z2034831520/FunModularKeyboard-Numpad/doc/image1.png

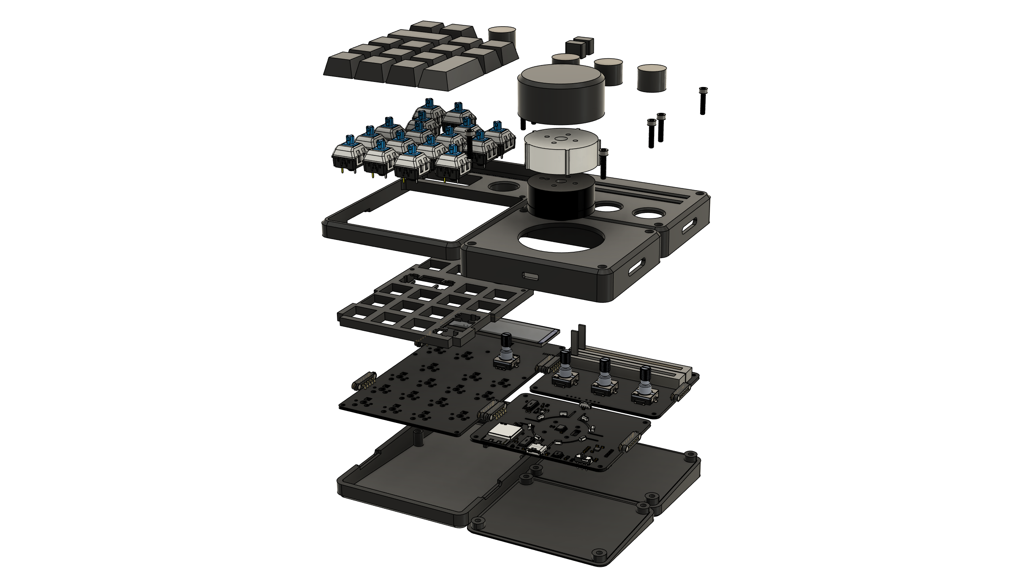
doc/image1.png
