z2034831520/FunModularKeyboard-Numpad/doc/image3.png

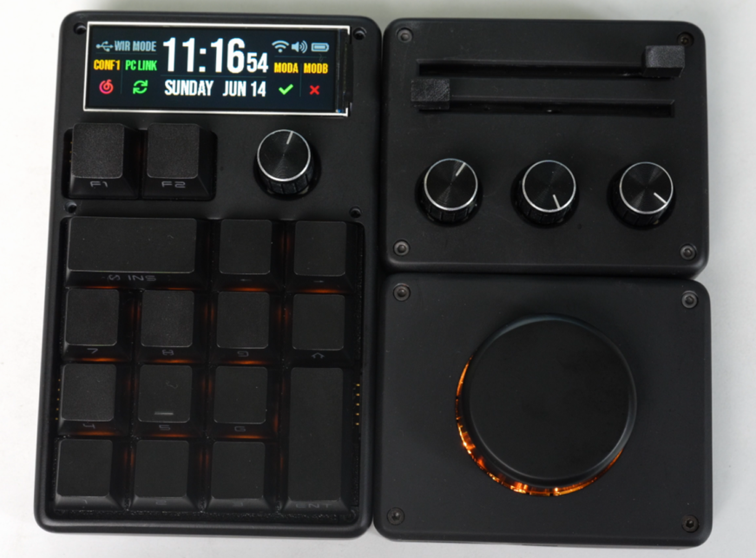
doc/image3.png
