z2034831520/FunModularKeyboard-Numpad/doc/image5.png

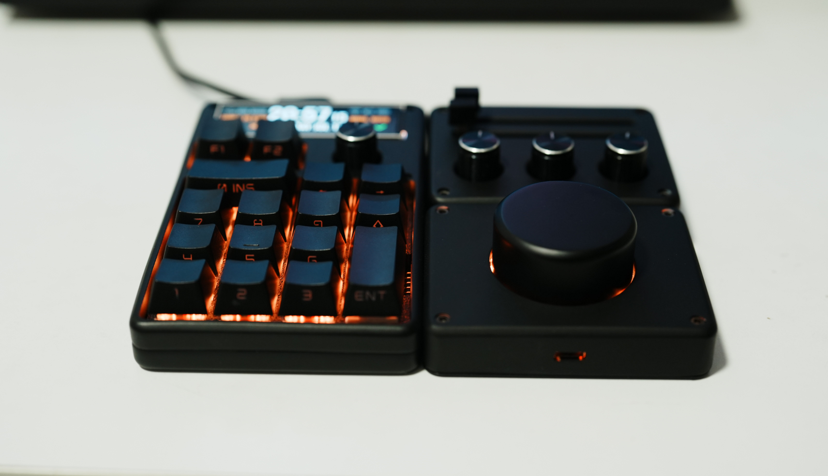
doc/image5.png
