z2034831520/FunModularKeyboard-Numpad/firmware/FunModularKeyboard/src/lvgl_setup.cpp

#include "lvgl_setup.h"
#include "display_config.h"
#include "nv3007_init.h"
#include <Arduino.h>
#include <lvgl.h>
#include <SPIFFS.h>
#include <TFT_eSPI.h>

namespace
{
    constexpr uint8_t kTftBacklightPwmChannel = 7;
    // Keep the LEDC configuration inside the ESP32-S3 timing budget.
    constexpr uint32_t kTftBacklightPwmFrequency = 5000;
    constexpr uint8_t kTftBacklightPwmResolution = 12;

    TFT_eSPI s_lcd;
    bool s_backlight_pwm_ready = false;
    bool s_tft_ready = false;
    bool s_spiffs_fs_registered = false;

    void nv3007_write_command(uint8_t command, const uint8_t *parameters, uint8_t parameter_count)
    {
        s_lcd.writecommand(command);
        for (uint8_t index = 0; index < parameter_count; ++index)
        {
            s_lcd.writedata(parameters[index]);
        }
    }

    void nv3007_initialize()
    {
        // TFT_eSPI initializes the SPI peripheral for us. Reset once more so the
        // generic bootstrap is discarded before applying the NV3007 sequence.
        pinMode(display_config::kResetPin, OUTPUT);
        digitalWrite(display_config::kResetPin, HIGH);
        delay(10);
        digitalWrite(display_config::kResetPin, LOW);
        delay(120);
        digitalWrite(display_config::kResetPin, HIGH);
        delay(120);

        s_lcd.startWrite();
        nv3007_write_command(0x28, nullptr, 0); // Display off during setup
        size_t position = 0;
        while (position < nv3007::kInitCommandsSize)
        {
            const uint8_t command = nv3007::kInitCommands[position++];
            const uint8_t parameter_count = nv3007::kInitCommands[position++];
            nv3007_write_command(command, &nv3007::kInitCommands[position], parameter_count);
            position += parameter_count;
        }
        nv3007_write_command(0x11, nullptr, 0); // Sleep out
        s_lcd.endWrite();
        delay(120);

        s_lcd.startWrite();
        const uint8_t landscape_rotation = 0x60; // MX | MV | RGB
        nv3007_write_command(0x36, &landscape_rotation, 1);
        s_lcd.endWrite();
    }

    String lvgl_spiffs_real_path(const char *path)
    {
        if (path == nullptr || path[0] == '\0')
        {
            return String("/");
        }
        if (path[0] == '/')
        {
            return String(path);
        }
        return String("/") + String(path);
    }

    void *lvgl_spiffs_open_cb(lv_fs_drv_t *drv, const char *path, lv_fs_mode_t mode)
    {
        LV_UNUSED(drv);
        const char *openMode = (mode == LV_FS_MODE_WR) ? FILE_WRITE : FILE_READ;
        File file = SPIFFS.open(lvgl_spiffs_real_path(path), openMode);
        if (!file)
        {
            return nullptr;
        }
        return new File(file);
    }

    lv_fs_res_t lvgl_spiffs_close_cb(lv_fs_drv_t *drv, void *file_p)
    {
        LV_UNUSED(drv);
        if (file_p == nullptr)
        {
            return LV_FS_RES_INV_PARAM;
        }
        File *file = static_cast<File *>(file_p);
        file->close();
        delete file;
        return LV_FS_RES_OK;
    }

    lv_fs_res_t lvgl_spiffs_read_cb(lv_fs_drv_t *drv, void *file_p, void *buf, uint32_t btr, uint32_t *br)
    {
        LV_UNUSED(drv);
        if (file_p == nullptr || buf == nullptr || br == nullptr)
        {
            return LV_FS_RES_INV_PARAM;
        }
        File *file = static_cast<File *>(file_p);
        *br = file->read(static_cast<uint8_t *>(buf), btr);
        return LV_FS_RES_OK;
    }

    lv_fs_res_t lvgl_spiffs_seek_cb(lv_fs_drv_t *drv, void *file_p, uint32_t pos, lv_fs_whence_t whence)
    {
        LV_UNUSED(drv);
        if (file_p == nullptr)
        {
            return LV_FS_RES_INV_PARAM;
        }
        File *file = static_cast<File *>(file_p);
        if (whence == LV_FS_SEEK_SET)
        {
            return file->seek(pos, SeekSet) ? LV_FS_RES_OK : LV_FS_RES_UNKNOWN;
        }
        if (whence == LV_FS_SEEK_CUR)
        {
            return file->seek(file->position() + pos, SeekSet) ? LV_FS_RES_OK : LV_FS_RES_UNKNOWN;
        }
        return file->seek(file->size() + pos, SeekSet) ? LV_FS_RES_OK : LV_FS_RES_UNKNOWN;
    }

    lv_fs_res_t lvgl_spiffs_tell_cb(lv_fs_drv_t *drv, void *file_p, uint32_t *pos_p)
    {
        LV_UNUSED(drv);
        if (file_p == nullptr || pos_p == nullptr)
        {
            return LV_FS_RES_INV_PARAM;
        }
        File *file = static_cast<File *>(file_p);
        *pos_p = file->position();
        return LV_FS_RES_OK;
    }

}

void lvgl_hold_backlight_off()
{
    // GPIO37 drives an active-low PNP switch. Hold it inactive before the
    // display stack is ready so uninitialized panel memory is never exposed.
    pinMode(display_config::kBacklightPin, OUTPUT);
    digitalWrite(display_config::kBacklightPin, display_config::kBacklightOffLevel);
}

void lvgl_enable_panel_output()
{
    if (!s_tft_ready)
    {
        return;
    }

    s_lcd.startWrite();
    nv3007_write_command(0x29, nullptr, 0); // Display on after first frame
    s_lcd.endWrite();
    delay(20);
}

void lvgl_set_backlight_brightness(uint8_t brightness_percent)
{
    const uint8_t clamped = brightness_percent > 100 ? 100 : brightness_percent;
    const uint32_t max_duty = (1UL << kTftBacklightPwmResolution) - 1UL;
    const uint32_t duty = (uint32_t)clamped * max_duty / 100UL;
    const uint32_t applied_duty = max_duty - duty;

    if (!s_backlight_pwm_ready)
    {
        pinMode(display_config::kBacklightPin, OUTPUT);
        digitalWrite(display_config::kBacklightPin, display_config::kBacklightOffLevel);
        const double configured_frequency = ledcSetup(kTftBacklightPwmChannel,
                                                      kTftBacklightPwmFrequency,
                                                      kTftBacklightPwmResolution);
        if (configured_frequency > 0.0)
        {
            ledcAttachPin(display_config::kBacklightPin, kTftBacklightPwmChannel);
            s_backlight_pwm_ready = true;
        }
    }

    if (s_backlight_pwm_ready)
    {
        ledcWrite(kTftBacklightPwmChannel, applied_duty);
    }
    else
    {
        digitalWrite(display_config::kBacklightPin,
                     clamped == 0 ? display_config::kBacklightOffLevel
                                  : display_config::kBacklightOnLevel);
    }
}

void lvgl_register_spiffs_fs()
{
    if (s_spiffs_fs_registered)
    {
        return;
    }

    static lv_fs_drv_t fs_drv;
    lv_fs_drv_init(&fs_drv);
    fs_drv.letter = 'S';
    fs_drv.open_cb = lvgl_spiffs_open_cb;
    fs_drv.close_cb = lvgl_spiffs_close_cb;
    fs_drv.read_cb = lvgl_spiffs_read_cb;
    fs_drv.seek_cb = lvgl_spiffs_seek_cb;
    fs_drv.tell_cb = lvgl_spiffs_tell_cb;
    lv_fs_drv_register(&fs_drv);
    s_spiffs_fs_registered = true;
}

void lvgl_setup()
{
    // 1. 初始化显示驱动
    lvgl_hold_backlight_off();
    s_lcd.begin();
    nv3007_initialize();
    s_tft_ready = true;
    s_lcd.fillScreen(TFT_BLACK);
    Serial.printf("LCD: NV3007 ready, %dx%d, SPI %ld Hz\n",
                  display_config::kDisplayWidth,
                  display_config::kDisplayHeight,
                  (long)display_config::kSpiFrequency);

    // 2. 初始化 LVGL
    lv_init();
    lvgl_register_spiffs_fs();

    // 3. 设置显示缓冲区
    static lv_color_t buf1[DISP_BUF_SIZE];
    static lv_color_t buf2[DISP_BUF_SIZE];
    static lv_disp_draw_buf_t draw_buf;
    lv_disp_draw_buf_init(&draw_buf, buf1, buf2, DISP_BUF_SIZE);

    // 4. 注册显示驱动
    static lv_disp_drv_t disp_drv;
    lv_disp_drv_init(&disp_drv);
    disp_drv.draw_buf = &draw_buf;
    disp_drv.flush_cb = my_disp_flush; // 实现这个函数
    disp_drv.hor_res = display_config::kDisplayWidth;
    disp_drv.ver_res = display_config::kDisplayHeight;
    lv_disp_drv_register(&disp_drv);

    // 5. 如果需要触摸屏，注册输入设备
    // static lv_indev_drv_t indev_drv;
    // lv_indev_drv_init(&indev_drv);
    // indev_drv.type = LV_INDEV_TYPE_POINTER;
    // indev_drv.read_cb = my_touchpad_read; // 实现这个函数
    // lv_indev_drv_register(&indev_drv);
}

// 显示刷新回调函数
void my_disp_flush(lv_disp_drv_t *disp, const lv_area_t *area, lv_color_t *color_p)
{
    uint32_t w = (area->x2 - area->x1 + 1);
    uint32_t h = (area->y2 - area->y1 + 1);

    if (s_tft_ready)
    {
        const uint16_t x1 = (uint16_t)area->x1 + display_config::kLandscapeXOffset;
        const uint16_t x2 = x1 + (uint16_t)w - 1;
        const uint16_t y1 = (uint16_t)area->y1 + display_config::kLandscapeYOffset;
        const uint16_t y2 = y1 + (uint16_t)h - 1;

        s_lcd.startWrite();
        s_lcd.writecommand(0x2A); // Column address set
        s_lcd.writedata(x1 >> 8);
        s_lcd.writedata(x1 & 0xFF);
        s_lcd.writedata(x2 >> 8);
        s_lcd.writedata(x2 & 0xFF);
        s_lcd.writecommand(0x2B); // Row address set
        s_lcd.writedata(y1 >> 8);
        s_lcd.writedata(y1 & 0xFF);
        s_lcd.writedata(y2 >> 8);
        s_lcd.writedata(y2 & 0xFF);
        s_lcd.writecommand(0x2C); // Memory write
        s_lcd.pushColors(reinterpret_cast<uint16_t*>(&color_p->full), w * h, true);
        s_lcd.endWrite();
    }

    lv_disp_flush_ready(disp);
}

// 触摸屏读取回调函数 (可选)
// bool my_touchpad_read(lv_indev_drv_t *indev_driver, lv_indev_data_t *data) {
//     // 实现触摸屏读取逻辑
//     return false;
// }
