z2034831520/FunModularKeyboard-Numpad/firmware/FunModularKeyboard/include/nv3007_init.h

#pragma once

#include <stddef.h>
#include <stdint.h>

namespace nv3007 {

// Command stream format: command, parameter count, parameters...
// Initialization values are for the 2.79-inch 142x428 NV3007 panel.
constexpr uint8_t kInitCommands[] = {
    0xFF, 1, 0xA5,
    0x9A, 1, 0x08,
    0x9B, 1, 0x08,
    0x9C, 1, 0xB0,
    0x9D, 1, 0x16,
    0x9E, 1, 0xC4,
    0x8F, 2, 0x55, 0x04,
    0x84, 1, 0x90,
    0x83, 1, 0x7B,
    0x85, 1, 0x33,
    0x60, 1, 0x00,
    0x70, 1, 0x00,
    0x61, 1, 0x02,
    0x71, 1, 0x02,
    0x62, 1, 0x04,
    0x72, 1, 0x04,
    0x6C, 1, 0x29,
    0x7C, 1, 0x29,
    0x6D, 1, 0x31,
    0x7D, 1, 0x31,
    0x6E, 1, 0x0F,
    0x7E, 1, 0x0F,
    0x66, 1, 0x21,
    0x76, 1, 0x21,
    0x68, 1, 0x3A,
    0x78, 1, 0x3A,
    0x63, 1, 0x07,
    0x73, 1, 0x07,
    0x64, 1, 0x05,
    0x74, 1, 0x05,
    0x65, 1, 0x02,
    0x75, 1, 0x02,
    0x67, 1, 0x23,
    0x77, 1, 0x23,
    0x69, 1, 0x08,
    0x79, 1, 0x08,
    0x6A, 1, 0x13,
    0x7A, 1, 0x13,
    0x6B, 1, 0x13,
    0x7B, 1, 0x13,
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
};

constexpr size_t kInitCommandsSize = sizeof(kInitCommands);

} // namespace nv3007
