z2034831520/FunModularKeyboard-Numpad/firmware/FunModularKeyboard_ModA/common.h

// UINT type definition
#ifndef _UINT_DEF_
#define _UINT_DEF_
typedef unsigned int UINT;
#endif  

// BYTE type definition
#ifndef _BYTE_DEF_
#define _BYTE_DEF_
typedef unsigned char BYTE;
#endif   


#ifndef E_OK
#define E_OK 						0x00
#endif   

#ifndef E_Already_Initialised
#define E_Already_Initialised 		0x01

#endif   
